rizett/PIGI_system/Technical drawings and CAD/Solidworks_drawings/PIGI4.3_Optode-Chamber-Support_PartG.SLDPRT

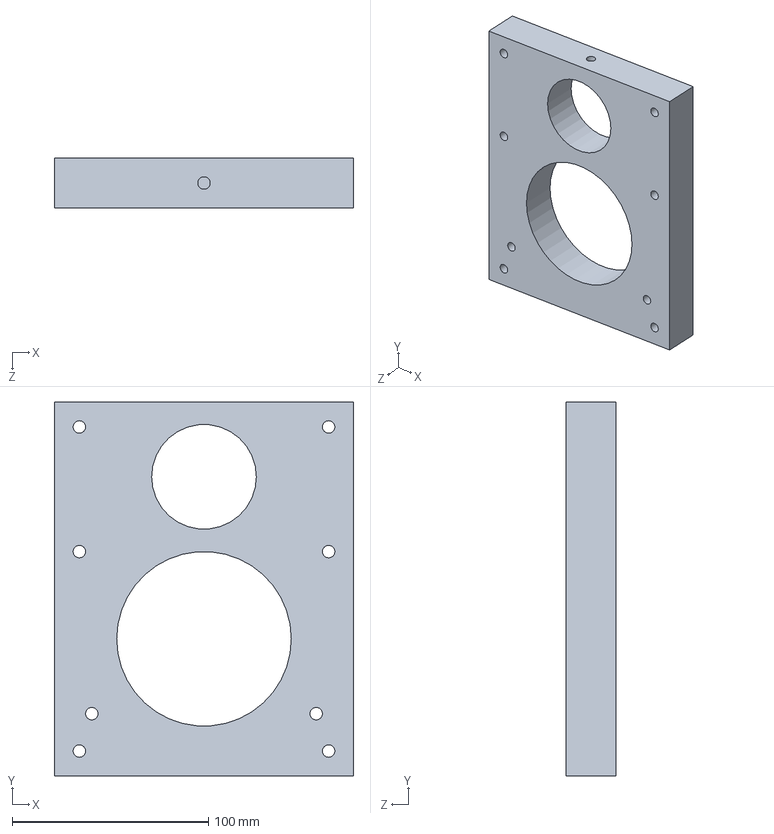
[picture p18: CAD file, 2020-06-26]
Technical drawings and CAD/Solidworks_drawings/PIGI4.3_Optode-Chamber-Support_PartG.SLDPRT
152.4 x 190.5 x 25.4 mm
