rizett/PIGI_system/Technical drawings and CAD/Solidworks_drawings/PIGI4.3_Check-Valve_Part25.SLDPRT

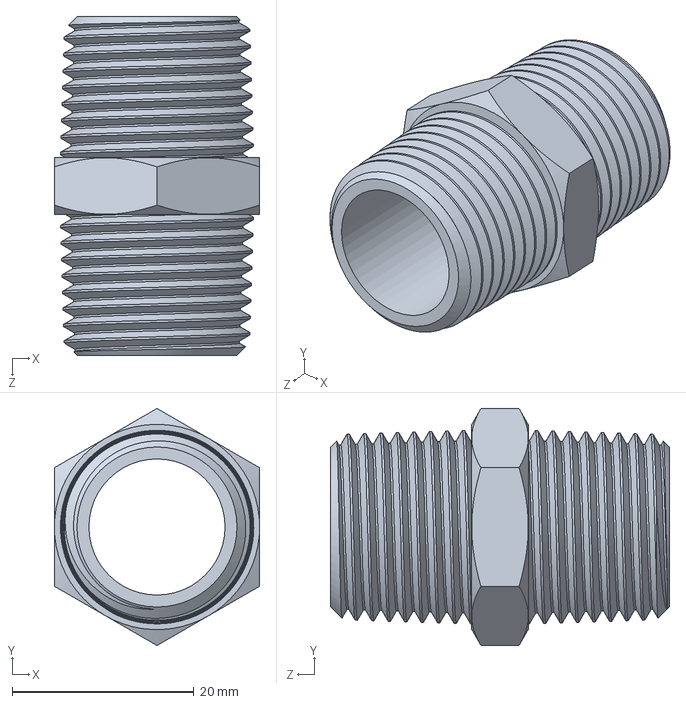
[picture p19: CAD file, 2020-06-26]
Technical drawings and CAD/Solidworks_drawings/PIGI4.3_Check-Valve_Part25.SLDPRT
22.6 x 26.1 x 37.3 mm
