rizett/PIGI_system/Technical drawings and CAD/Solidworks_drawings/PIGI4.3_Check-Valve_Part23.SLDPRT

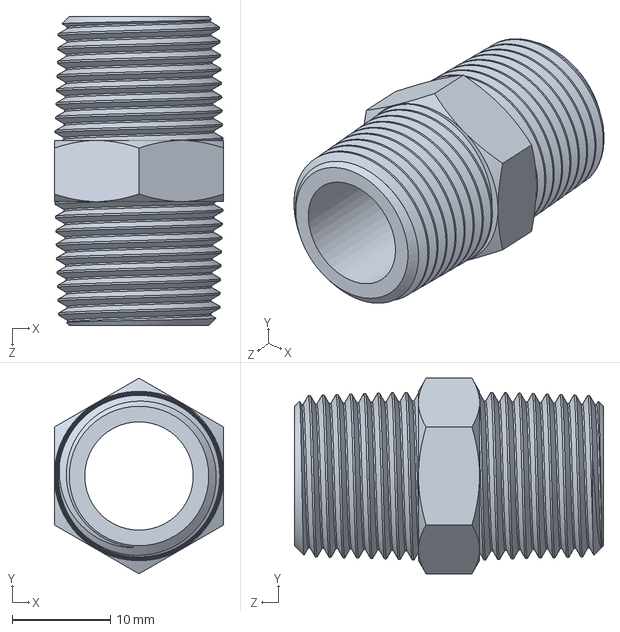
[picture p20: CAD file, 2020-06-26]
Technical drawings and CAD/Solidworks_drawings/PIGI4.3_Check-Valve_Part23.SLDPRT
17.3 x 19.9 x 31.5 mm
