rizett/PIGI_system/Technical drawings and CAD/Solidworks_drawings/PIGI4.3_Debubbler-Tube_Part8.SLDPRT

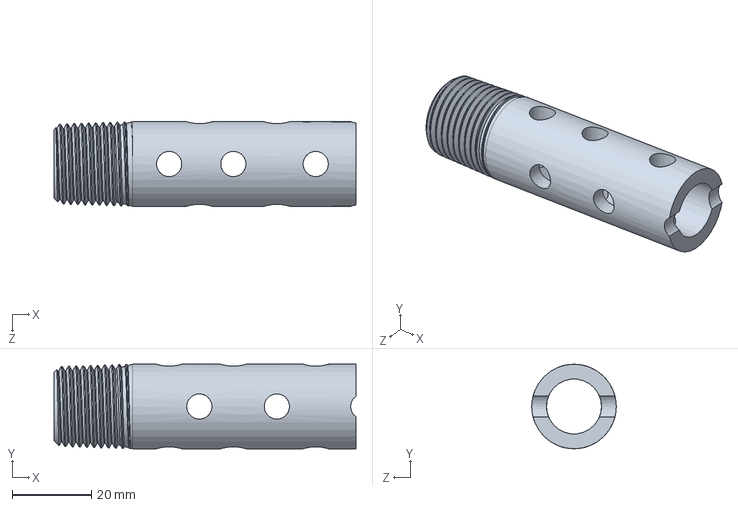
[picture p21: CAD file, 2020-06-26]
Technical drawings and CAD/Solidworks_drawings/PIGI4.3_Debubbler-Tube_Part8.SLDPRT
76.2 x 21.3 x 21.3 mm
