rizett/PIGI_system/Technical drawings and CAD/Solidworks_drawings/PIGI4.3_Primary-Flow-Meter_Part5.SLDPRT

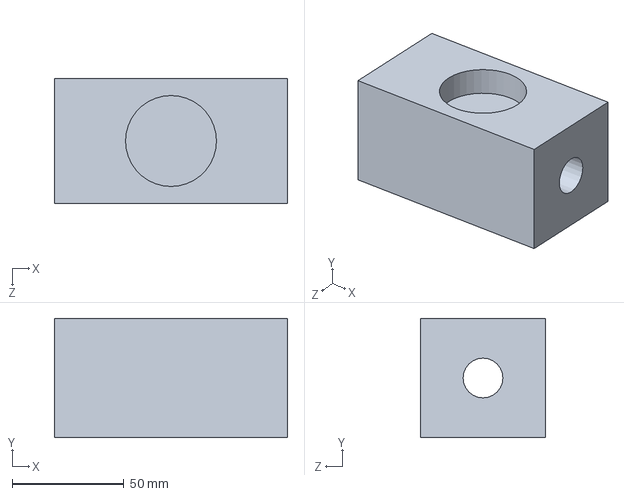
[picture p22: CAD file, 2020-06-26]
Technical drawings and CAD/Solidworks_drawings/PIGI4.3_Primary-Flow-Meter_Part5.SLDPRT
104.1 x 53.3 x 55.9 mm
