rizett/PIGI_system/Technical drawings and CAD/Solidworks_drawings/PIGI4.3_Optode-chamber-tube_PartC.SLDPRT

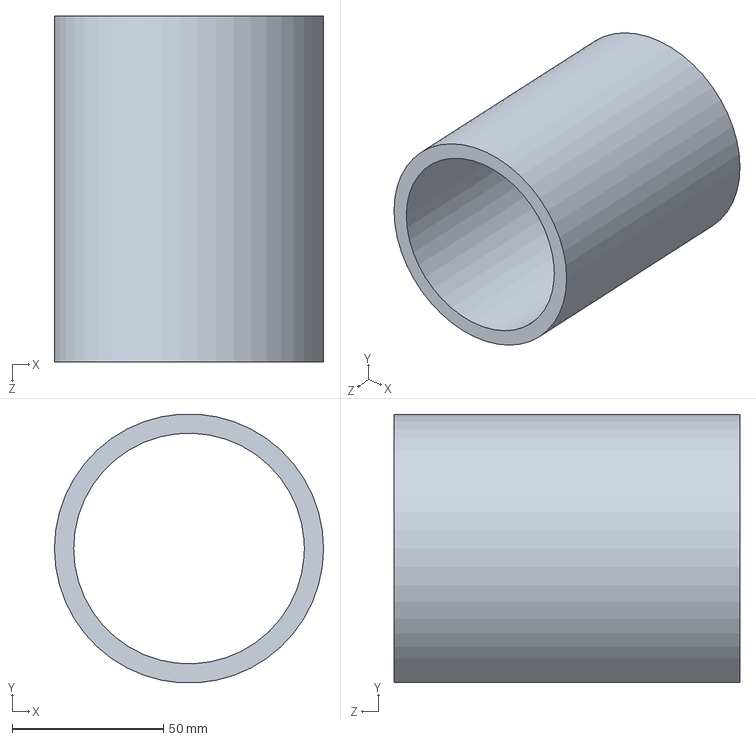
[picture p23: CAD file, 2020-06-26]
Technical drawings and CAD/Solidworks_drawings/PIGI4.3_Optode-chamber-tube_PartC.SLDPRT
88.9 x 88.7 x 114.3 mm
