rizett/PIGI_system/Technical drawings and CAD/Solidworks_drawings/PIGI4.3_9in-SS-rod_Part32.SLDPRT

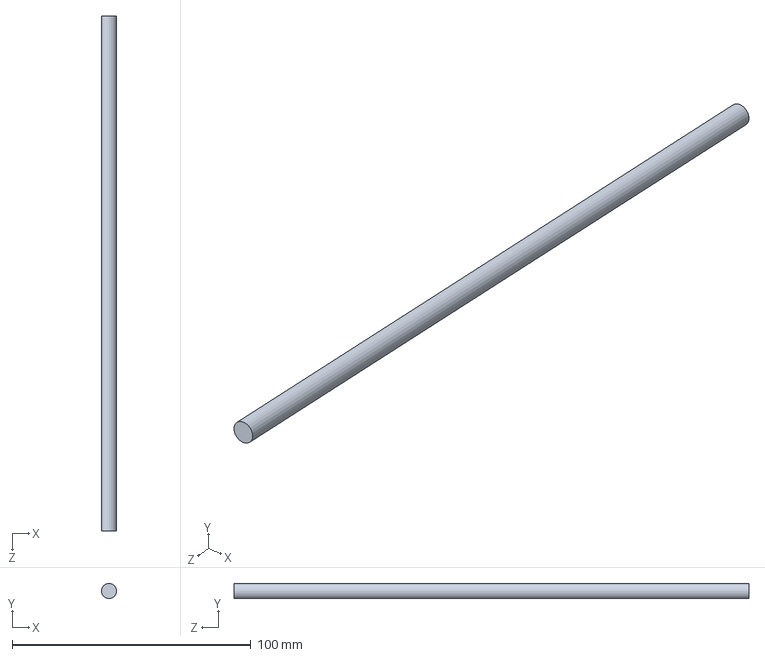
[picture p24: CAD file, 2020-06-26]
Technical drawings and CAD/Solidworks_drawings/PIGI4.3_9in-SS-rod_Part32.SLDPRT
6.35 x 6.35 x 215.9 mm
