rizett/PIGI_system/Technical drawings and CAD/Solidworks_drawings/PIGI4.3_Debubbler-Bulkhead-Connector_Part9.SLDPRT

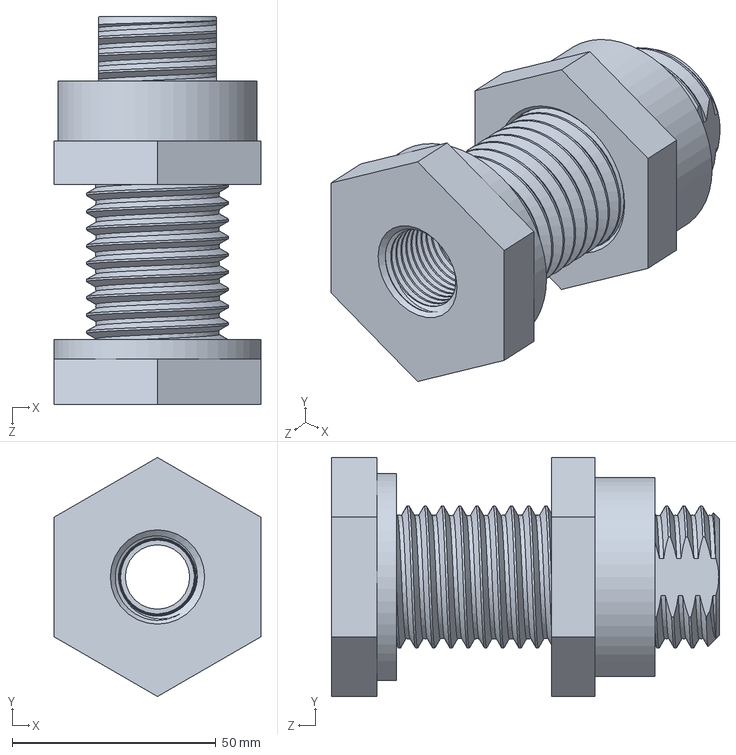
[picture p25: CAD file, 2020-06-26]
Technical drawings and CAD/Solidworks_drawings/PIGI4.3_Debubbler-Bulkhead-Connector_Part9.SLDPRT
50.8 x 58.7 x 95.2 mm
