rizett/PIGI_system/Technical drawings and CAD/Solidworks_drawings/PIGI4.3_mini-TDGP_Part2.SLDPRT

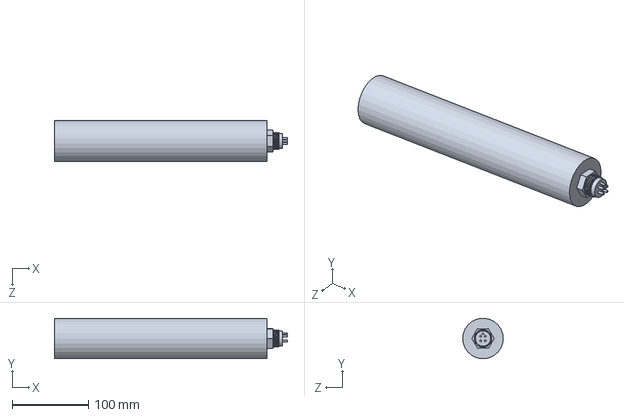
[picture p26: CAD file, 2020-06-26]
Technical drawings and CAD/Solidworks_drawings/PIGI4.3_mini-TDGP_Part2.SLDPRT
306.1 x 53.0 x 53.3 mm
