rizett/PIGI_system/Technical drawings and CAD/Solidworks_drawings/PIGI4.3_Optode_Part1.SLDPRT

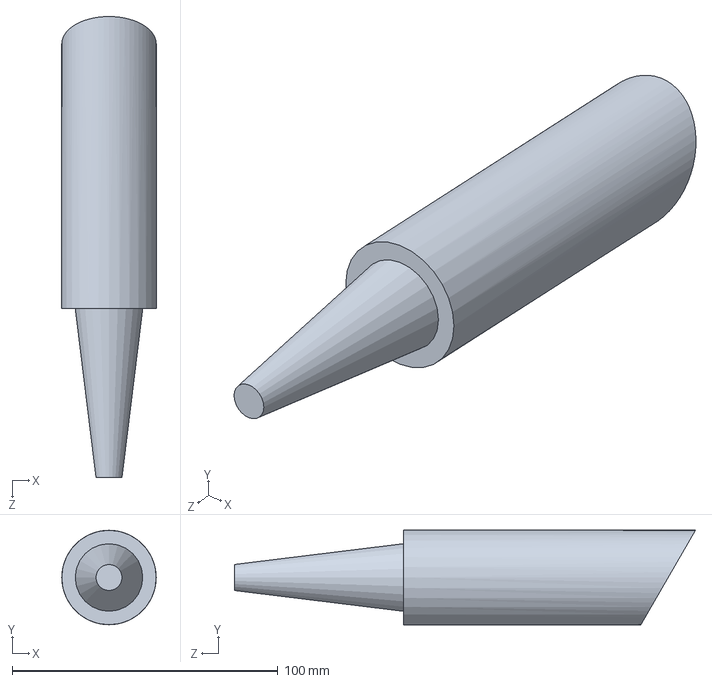
[picture p27: CAD file, 2020-06-26]
Technical drawings and CAD/Solidworks_drawings/PIGI4.3_Optode_Part1.SLDPRT
35.6 x 35.6 x 173.4 mm
