rizett/PIGI_system/Technical drawings and CAD/Solidworks_drawings/PIGI4.3_Optode-Support_PartK.SLDPRT

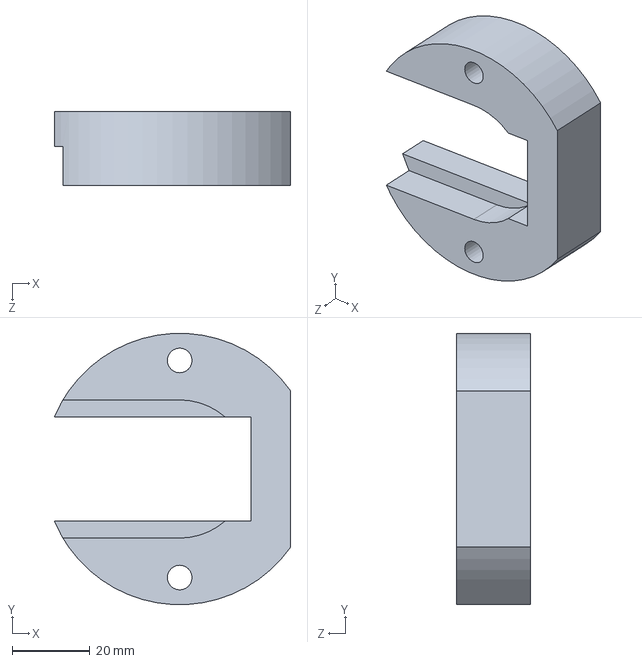
[picture p28: CAD file, 2020-06-26]
Technical drawings and CAD/Solidworks_drawings/PIGI4.3_Optode-Support_PartK.SLDPRT
60.9 x 69.7 x 19.1 mm
