rizett/PIGI_system/Technical drawings and CAD/Solidworks_drawings/PIGI4.3_Pipe-Adapter_Part24.SLDPRT

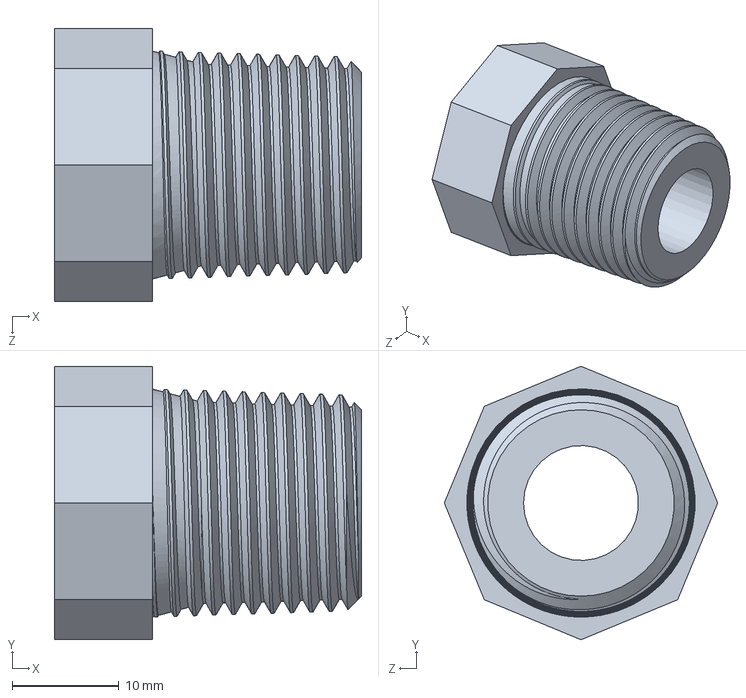
[picture p29: CAD file, 2020-06-26]
Technical drawings and CAD/Solidworks_drawings/PIGI4.3_Pipe-Adapter_Part24.SLDPRT
28.7 x 25.6 x 25.6 mm
