rizett/PIGI_system/Technical drawings and CAD/Solidworks_drawings/PIGI4.3_Pelican-Case-2720-base_Part7.SLDPRT

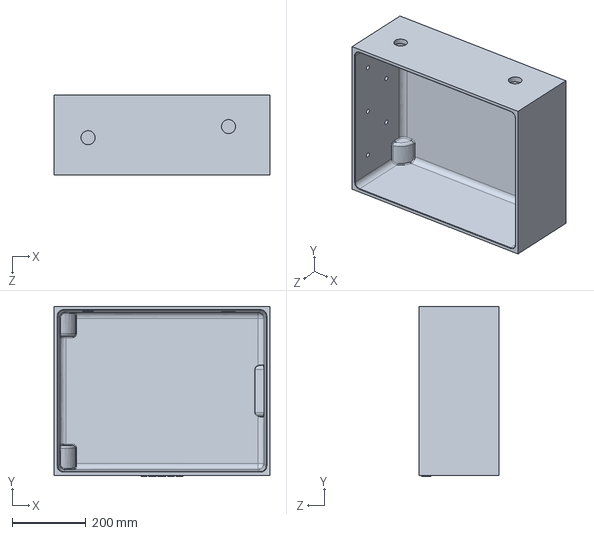
[picture p30: CAD file, 2020-06-26]
Technical drawings and CAD/Solidworks_drawings/PIGI4.3_Pelican-Case-2720-base_Part7.SLDPRT
584.2 x 460.4 x 215.9 mm
