rizett/PIGI_system/Technical drawings and CAD/Solidworks_drawings/PIGI4.3_Primary-chamber-Outflow-Oring_Part17.SLDPRT

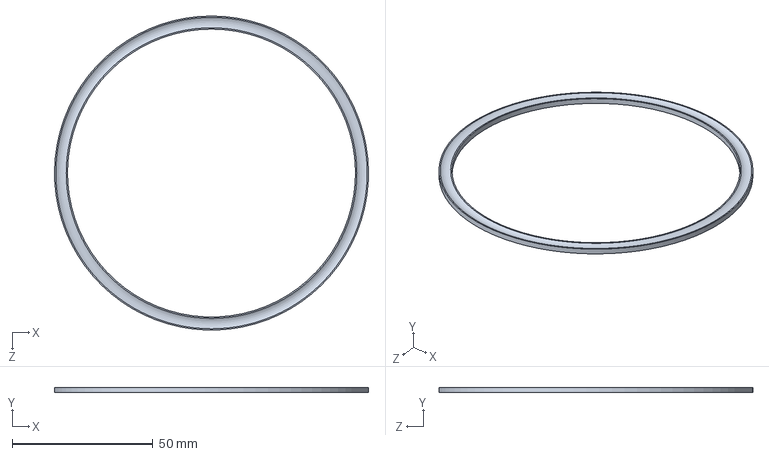
[picture p31: CAD file, 2020-06-26]
Technical drawings and CAD/Solidworks_drawings/PIGI4.3_Primary-chamber-Outflow-Oring_Part17.SLDPRT
111.6 x 1.93 x 111.6 mm
