rizett/PIGI_system/Technical drawings and CAD/Solidworks_drawings/PIGI4.3_Compression-Pads_Part36.SLDPRT

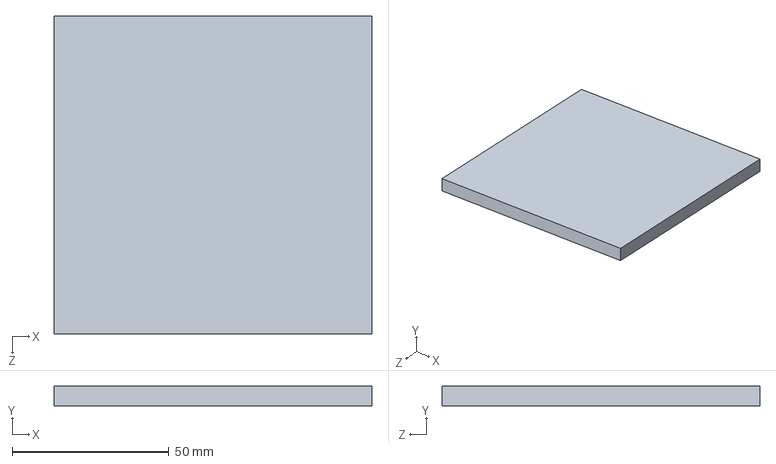
[picture p33: CAD file, 2020-06-26]
Technical drawings and CAD/Solidworks_drawings/PIGI4.3_Compression-Pads_Part36.SLDPRT
101.6 x 6.35 x 101.6 mm
