rizett/PIGI_system/Technical drawings and CAD/Solidworks_drawings/PIGI4.3_Elbow-Valve_Part19.SLDPRT

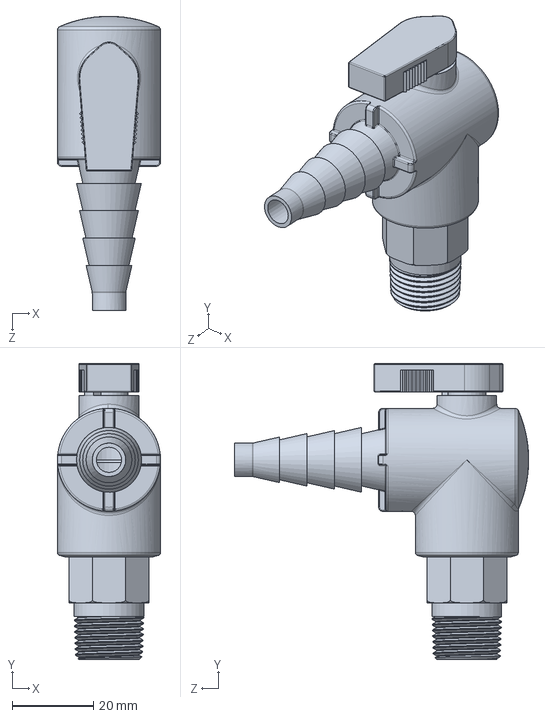
[picture p34: CAD file, 2020-06-26]
Technical drawings and CAD/Solidworks_drawings/PIGI4.3_Elbow-Valve_Part19.SLDPRT
25.4 x 72.9 x 72.5 mm
