rizett/PIGI_system/Technical drawings and CAD/Solidworks_drawings/PIGI4.3_Optode-Chamber-Outflow-Cap_PartI.SLDPRT

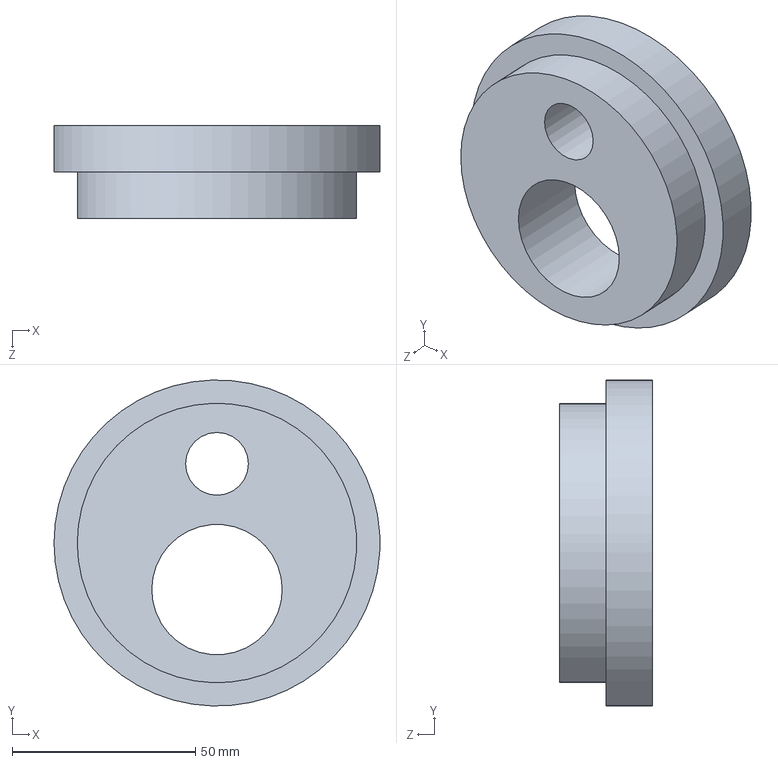
[picture p35: CAD file, 2020-06-26]
Technical drawings and CAD/Solidworks_drawings/PIGI4.3_Optode-Chamber-Outflow-Cap_PartI.SLDPRT
88.9 x 88.9 x 25.4 mm
