rizett/PIGI_system/Technical drawings and CAD/Solidworks_drawings/PIGI4.3_Chamber-Base-PartA.SLDPRT

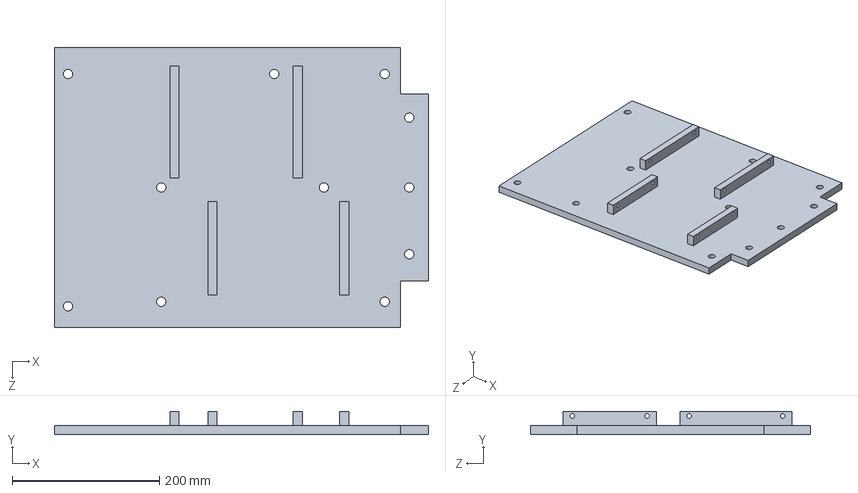
[picture p36: CAD file, 2020-06-26]
Technical drawings and CAD/Solidworks_drawings/PIGI4.3_Chamber-Base-PartA.SLDPRT
508.0 x 31.8 x 381.0 mm
